TomasTT7/TT7D-Tracker/Software/AVR_UBLOX.h

/*
	GNSS Modules
		u-blox MAX-M8Q		Protocol 18.00 (Firmware 3.01)		concurrent GNSS reception (GPS, Galileo, GLONASS, BeiDou)
		u-blox MAX-7Q		Protocol 14.00 (Firmware 1.00)		single GNSS reception (GPS, GLONASS)
		Bwin GM10			Protocol 14.00 (Firmware 1.00)		single GNSS reception (GPS, GLONASS)
		
	Default Output
		9600 baud, 8 bits, no parity bit, 1 stop bit
*/


#ifndef AVR_UBLOX_H
#define AVR_UBLOX_H


#include <avr/pgmspace.h>
#include "AVR_UART.h"


/* Set Timepulse 12MHz in UBX-CFG-TP5 */
PROGMEM static const uint8_t timepulse12MHz[40]				= {0xB5, 0x62, 0x06, 0x31, 0x20, 0x00, 0x00, 0x01, 0x00, 0x00, 0x00, 0x00, 0x00, 0x00, 0x00, 0x1B,
															   0xB7, 0x00, 0x01, 0x00, 0x00, 0x00, 0x00, 0x00, 0x00, 0x80, 0x00, 0x00, 0x00, 0x00, 0x00, 0x00,
															   0x00, 0x00, 0x6B, 0x00, 0x00, 0x00, 0x16, 0x51};
/* Set Timepulse 8MHz in UBX-CFG-TP5 */
PROGMEM static const uint8_t timepulse8MHz[40]				= {0xB5, 0x62, 0x06, 0x31, 0x20, 0x00, 0x00, 0x01, 0x00, 0x00, 0x00, 0x00, 0x00, 0x00, 0x00, 0x12,
															   0x7A, 0x00, 0x01, 0x00, 0x00, 0x00, 0x00, 0x00, 0x00, 0x80, 0x00, 0x00, 0x00, 0x00, 0x00, 0x00,
															   0x00, 0x00, 0x6B, 0x00, 0x00, 0x00, 0xD0, 0x44};
/* Set Timepulse OFF in UBX-CFG-TP5 */
PROGMEM static const uint8_t timepulseOFF[40]				= {0xB5, 0x62, 0x06, 0x31, 0x20, 0x00, 0x00, 0x01, 0x00, 0x00, 0x00, 0x00, 0x00, 0x00, 0x00, 0x12,
															   0x7A, 0x00, 0x01, 0x00, 0x00, 0x00, 0x00, 0x00, 0x00, 0x80, 0x00, 0x00, 0x00, 0x00, 0x00, 0x00,
															   0x00, 0x00, 0x6A, 0x00, 0x00, 0x00, 0xCF, 0x40};
/* Set NMEA output ON/OFF in UBX-CFG-PRT */
PROGMEM static const uint8_t setNMEAoff[28]					= {0xB5, 0x62, 0x06, 0x00, 0x14, 0x00, 0x01, 0x00, 0x00, 0x00, 0xD0, 0x08, 0x00, 0x00, 0x80, 0x25,
															   0x00, 0x00, 0x07, 0x00, 0x01, 0x00, 0x00, 0x00, 0x00, 0x00, 0xA0, 0xA9};
PROGMEM static const uint8_t setNMEAon[28]					= {0xB5, 0x62, 0x06, 0x00, 0x14, 0x00, 0x01, 0x00, 0x00, 0x00, 0xD0, 0x08, 0x00, 0x00, 0x80, 0x25,
															   0x00, 0x00, 0x07, 0x00, 0x03, 0x00, 0x00, 0x00, 0x00, 0x00, 0xA2, 0xB5};
/* Set Message Rate in UBX-CFG-MSG */
PROGMEM static const uint8_t setGGArateOFF[16]				= {0xB5, 0x62, 0x06, 0x01, 0x08, 0x00, 0xF0, 0x00, 0x00, 0x00, 0x00, 0x00, 0x00, 0x00, 0xFF, 0x23};
PROGMEM static const uint8_t setGLLrateOFF[16]				= {0xB5, 0x62, 0x06, 0x01, 0x08, 0x00, 0xF0, 0x01, 0x00, 0x00, 0x00, 0x00, 0x00, 0x00, 0x00, 0x2A};
PROGMEM static const uint8_t setGSArateOFF[16]				= {0xB5, 0x62, 0x06, 0x01, 0x08, 0x00, 0xF0, 0x02, 0x00, 0x00, 0x00, 0x00, 0x00, 0x00, 0x01, 0x31};
PROGMEM static const uint8_t setGSVrateOFF[16]				= {0xB5, 0x62, 0x06, 0x01, 0x08, 0x00, 0xF0, 0x03, 0x00, 0x00, 0x00, 0x00, 0x00, 0x00, 0x02, 0x38};
PROGMEM static const uint8_t setRMCrateOFF[16]				= {0xB5, 0x62, 0x06, 0x01, 0x08, 0x00, 0xF0, 0x04, 0x00, 0x00, 0x00, 0x00, 0x00, 0x00, 0x03, 0x3F};
PROGMEM static const uint8_t setVTGrateOFF[16]				= {0xB5, 0x62, 0x06, 0x01, 0x08, 0x00, 0xF0, 0x05, 0x00, 0x00, 0x00, 0x00, 0x00, 0x00, 0x04, 0x46};
/* Set Airborne Dynamic Model in UBX-CFG-NAV5 */
PROGMEM static const uint8_t setDynamicModelAirborne[44]	= {0xB5, 0x62, 0x06, 0x24, 0x24, 0x00, 0xFF, 0xFF, 0x06, 0x03, 0x00, 0x00, 0x00, 0x00, 0x10, 0x27,
															   0x00, 0x00, 0x05, 0x00, 0xFA, 0x00, 0xFA, 0x00, 0x64, 0x00, 0x2C, 0x01, 0x00, 0x3C, 0x00, 0x00,
															   0x00, 0x00, 0x00, 0x00, 0x00, 0x00, 0x00, 0x00, 0x00, 0x00, 0x52, 0xE8};
/* Set Backup mode for infinite duration in UBX-RXM-PMREQ */
PROGMEM static const uint8_t setBackupMode[16]				= {0xB5, 0x62, 0x02, 0x41, 0x08, 0x00, 0x00, 0x00, 0x00, 0x00, 0x02, 0x00, 0x00, 0x00, 0x4D, 0x3B};
/* Set Software backup in UBX-CFG-PWR (min. protocol 15 - GM10 protocol 14) */
PROGMEM static const uint8_t setSwBackupMode[16]			= {0xB5, 0x62, 0x06, 0x57, 0x08, 0x00, 0x01, 0x00, 0x00, 0x00, 0x50, 0x4B, 0x43, 0x42, 0x86, 0x46};
/* Set Continuous Mode in UBX-CFG-RXM */
PROGMEM static const uint8_t setContinuousMode[10]			= {0xB5, 0x62, 0x06, 0x11, 0x02, 0x00, 0x08, 0x00, 0x21, 0x91};
/* Request UBX-NAV-PVT (min. protocol 15 - GM10 protocol 14) */
/* response length: MAX-M8 100 bytes, GM10 92 bytes */
PROGMEM static const uint8_t requestPVT[8]					= {0xB5, 0x62, 0x01, 0x07, 0x00, 0x00, 0x08, 0x19};
/* Request UBX-CFG-NAV5 */
PROGMEM static const uint8_t requestNAV5[8]					= {0xB5, 0x62, 0x06, 0x24, 0x00, 0x00, 0x2A, 0x84};
/* Save Current Configuration in UBX-CFG-CFG */
PROGMEM static const uint8_t saveConfiguration[21]			= {0xB5, 0x62, 0x06, 0x09, 0x0D, 0x00, 0x00, 0x00, 0x00, 0x00, 0xFF, 0xFF, 0x00, 0x00, 0x00, 0x00,
															   0x00, 0x00, 0x01, 0x1B, 0xA9};
/* Dummy Byte */
PROGMEM static const uint8_t dummyByte[1]					= {0xFF};
/* Requset GPGGA Message. */
PROGMEM static const uint8_t requestGPGGA[15]				= "$EIGPQ,GGA*27\r\n";


// Functions
void UBLOX_send_msg(const uint8_t * buff, uint8_t len);
uint8_t UBLOX_receive_msg(uint8_t * buffer, uint8_t len, uint8_t nmea);
uint8_t UBLOX_verify_checksum(uint8_t *buff, uint8_t len);
void UBLOX_parse_0107(uint8_t * buffer, uint16_t * year, uint8_t * month, uint8_t * day, uint8_t * hour,
					  uint8_t * min, uint8_t * sec, uint8_t * valid, uint8_t * fixType, uint8_t * gnssFixOK,
					  uint8_t * psmState, uint8_t * numSV, float * lon, float * lat, int32_t * hMSL,
					  uint32_t * hAcc, uint32_t * vAcc, uint16_t * pDOP);
void UBLOX_parse_0624(uint8_t * buffer, uint8_t * model);
void UBLOX_parse_GPGGA(uint8_t * buffer, uint8_t * hour, uint8_t * min, uint8_t * sec, float * lat, float * lon,
					   int32_t * alt, uint8_t * numSV, uint8_t * quality, uint16_t * hdop);


#endif // AVR_UBLOX_H_
